Rookwork/saucer-diy-voyager-trackpad/readme_assets/heatshrink.jpeg

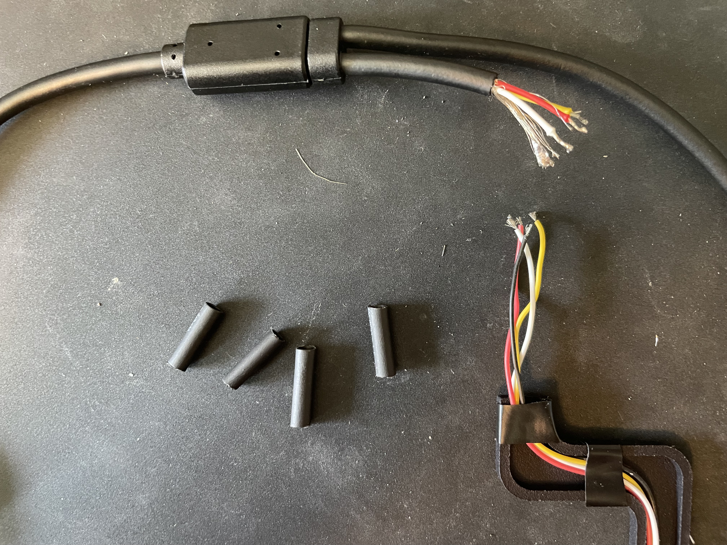
readme_assets/heatshrink.jpeg
