Rookwork/saucer-diy-voyager-trackpad/readme_assets/heatshrink_prep.jpeg

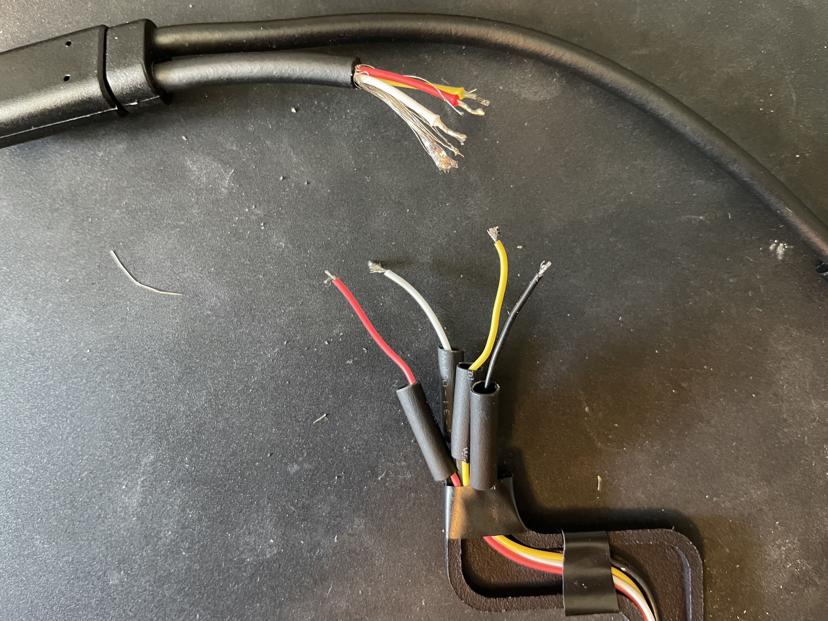
readme_assets/heatshrink_prep.jpeg
